emfcamp/tidal-docs/images/image_2022_05_06T06_09_14_036Z.png

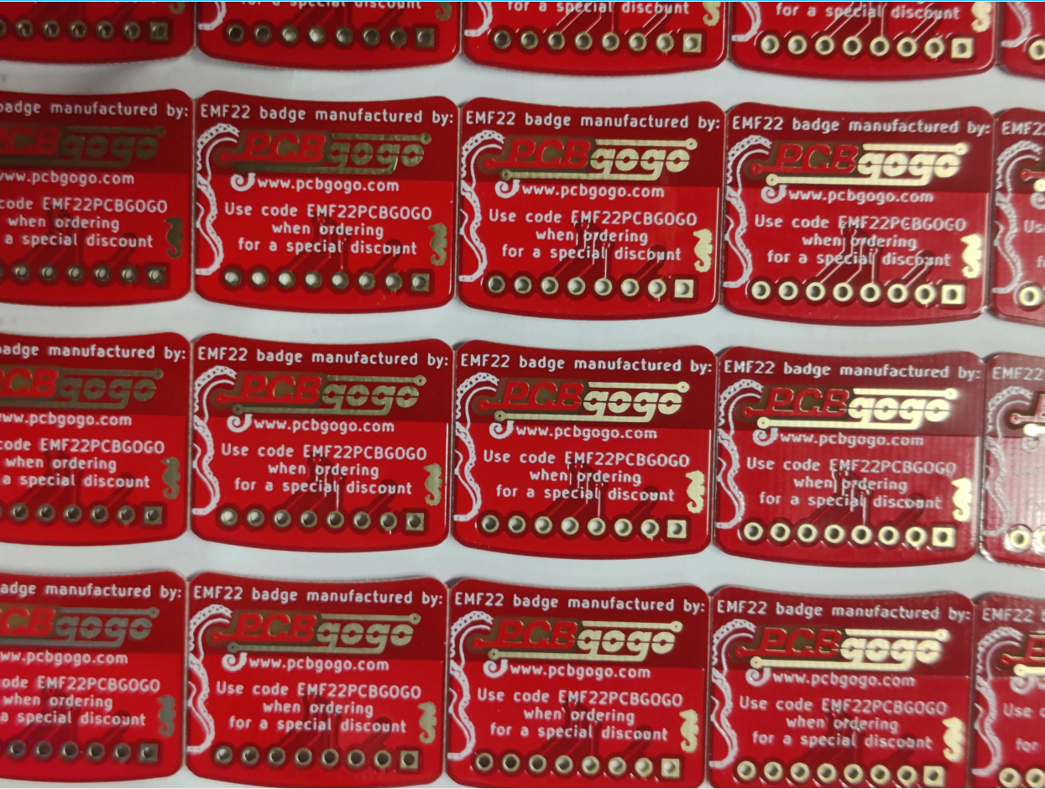
images/image_2022_05_06T06_09_14_036Z.png
