emfcamp/tidal-docs/images/image_2022_05_06T06_09_29_406Z.png

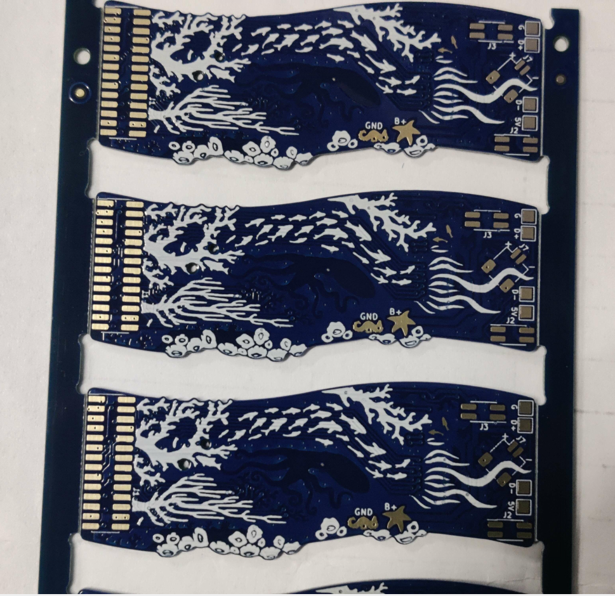
images/image_2022_05_06T06_09_29_406Z.png
