emfcamp/tidal-docs/images/image_2022_05_06T06_10_28_530Z.png

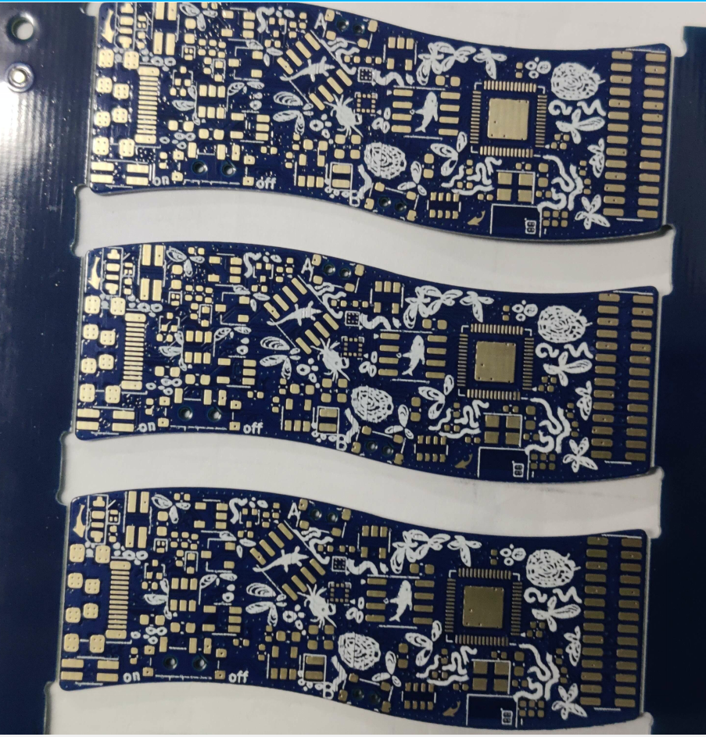
images/image_2022_05_06T06_10_28_530Z.png
