emfcamp/tidal-docs/images/image_2022_05_06T06_19_09_443Z.png

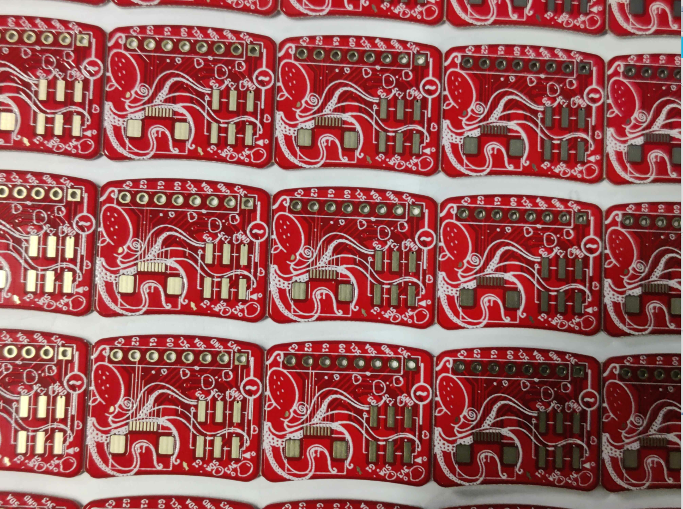
images/image_2022_05_06T06_19_09_443Z.png
