emfcamp/tidal-docs/images/tidal-full-transparent-annotated.png

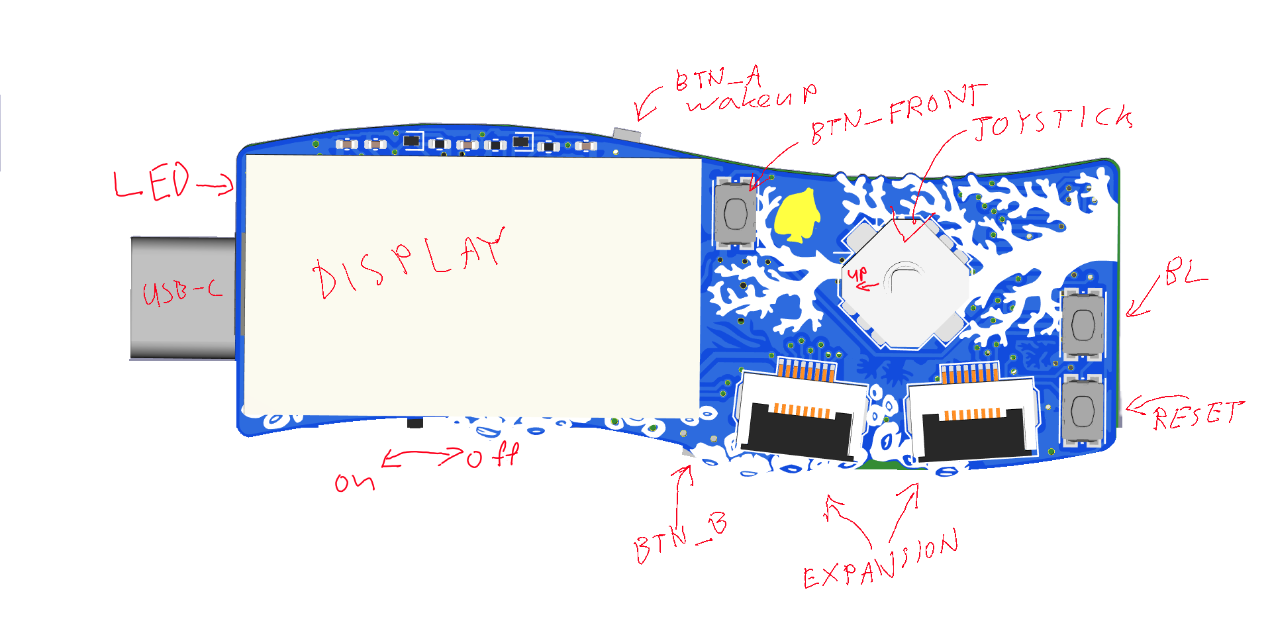
images/tidal-full-transparent-annotated.png
