emfcamp/tidal-docs/images/tidal-full-transparent.png

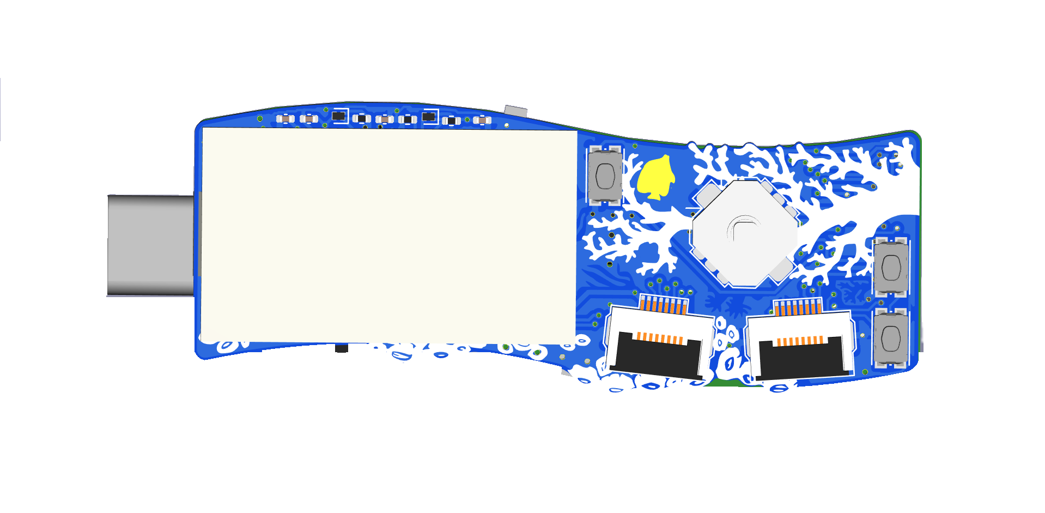
images/tidal-full-transparent.png
